ky-brah/UNLV-ATLAS-1/img/cubelol.jpeg

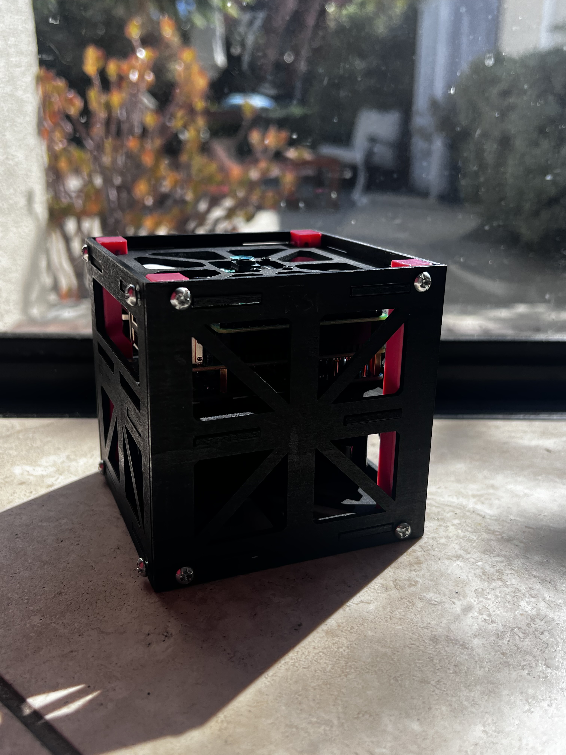
img/cubelol.jpeg
