ky-brah/UNLV-ATLAS-1/img/eyeseeyou.jpeg

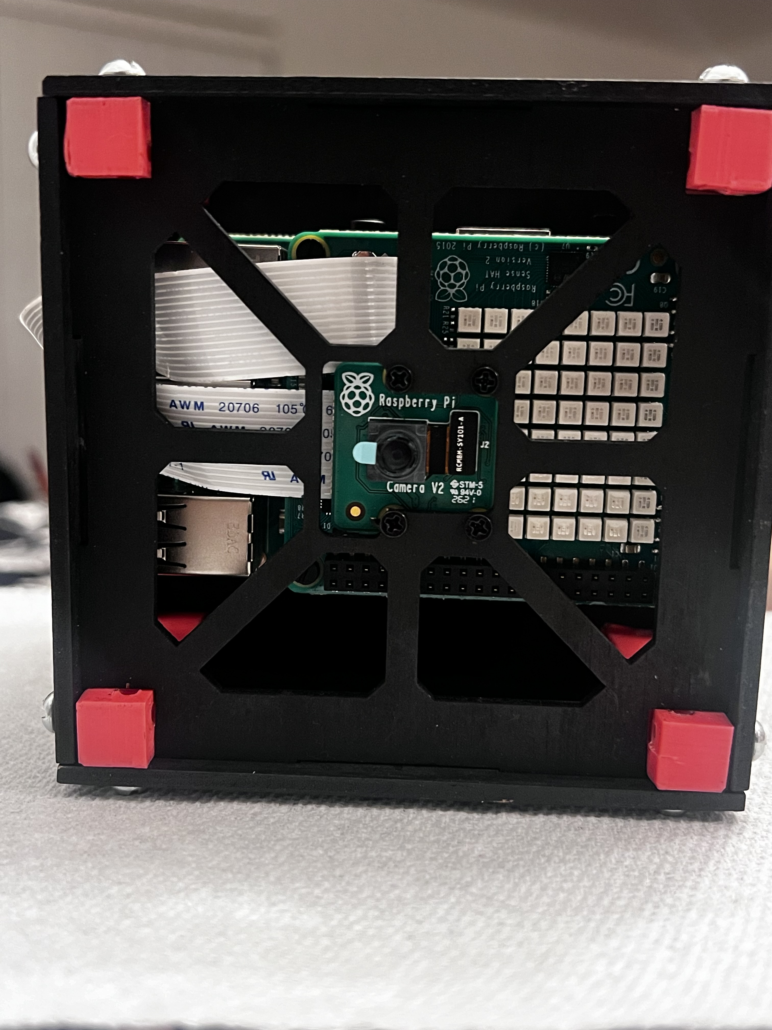
img/eyeseeyou.jpeg
