ky-brah/UNLV-ATLAS-1/img/ss25.jpeg

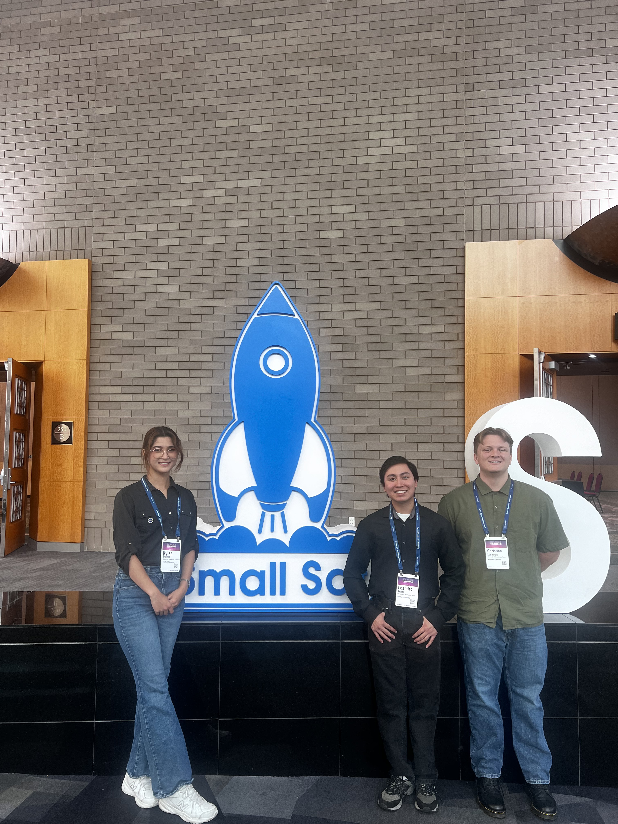
img/ss25.jpeg
